radiolok/midi2aux/hw/kicad/analog_in.kicad_sch

## KiCad design hw/kicad/analog_in.kicad_sch (2026-10-06)

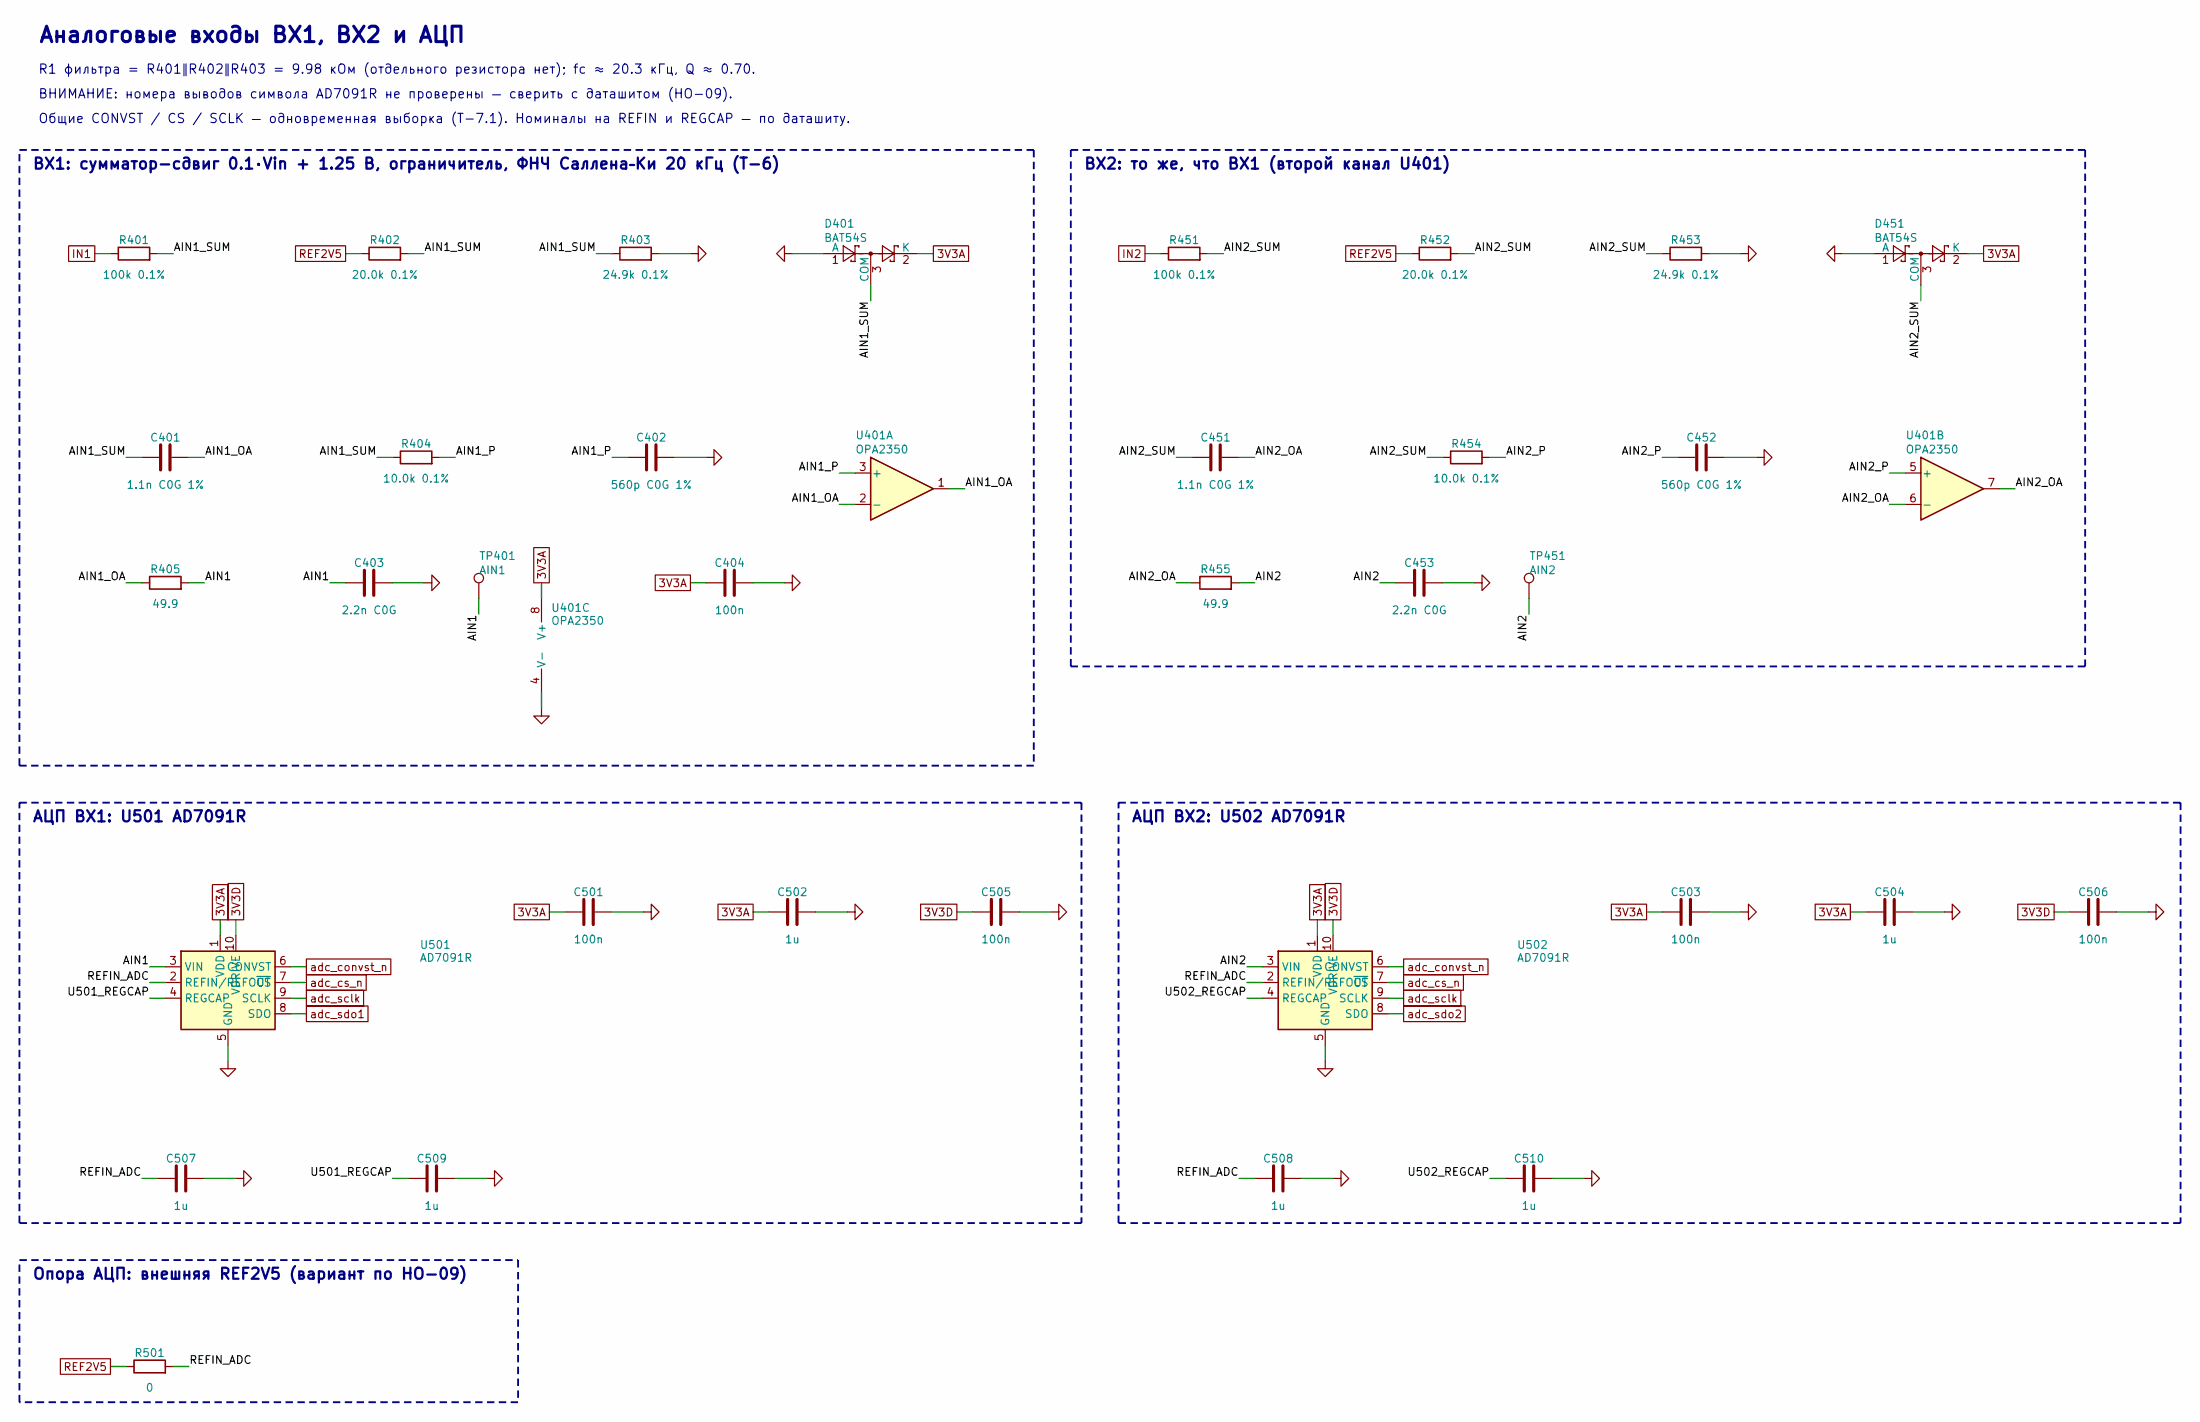
[picture p46: schematic analog_in.kicad_sch]

Parts:
C401, C451: 1.1n C0G 1%; C_0603_1608Metric
C402, C452: 560p C0G 1%; C_0603_1608Metric
C403, C453: 2.2n C0G; C_0603_1608Metric
C404, C501, C503, C505, C506: 100n; C_0603_1608Metric
C502, C504, C507, C508, C509, C510: 1u; C_0603_1608Metric
D401, D451: BAT54S; SOT-23
R401, R451: 100k 0.1%; R_0805_2012Metric
R402, R452: 20.0k 0.1%; R_0603_1608Metric
R403, R453: 24.9k 0.1%; R_0603_1608Metric
R404, R454: 10.0k 0.1%; R_0603_1608Metric
R405, R455: 49.9; R_0603_1608Metric
R501: 0; R_0603_1608Metric
TP401: AIN1; TestPoint_Pad_D1.5mm
TP451: AIN2; TestPoint_Pad_D1.5mm
U401: OPA2350; SOIC-8_3.9x4.9mm_P1.27mm
U501, U502: AD7091R; MSOP-10_3x3mm_P0.5mm

Connections:
3V3A: C404.1, C501.1, C502.1, C503.1, C504.1, D401.2 (K), D451.2 (K), U401.8 (V+), U501.1 (VDD), U502.1 (VDD)
3V3D: C505.1, C506.1, U501.10 (VDRIVE), U502.10 (VDRIVE)
AIN1: C403.1, R405.2, TP401.1, U501.3 (VIN)
AIN1_OA: C401.2, R405.1, U401.1, U401.2 (-)
AIN1_P: C402.1, R404.2, U401.3 (+)
AIN1_SUM: C401.1, D401.3 (COM), R401.2, R402.2, R403.1, R404.1
AIN2: C453.1, R455.2, TP451.1, U502.3 (VIN)
AIN2_OA: C451.2, R455.1, U401.6 (-), U401.7
AIN2_P: C452.1, R454.2, U401.5 (+)
AIN2_SUM: C451.1, D451.3 (COM), R451.2, R452.2, R453.1, R454.1
GND: C402.2, C403.2, C404.2, C452.2, C453.2, C501.2, C502.2, C503.2, C504.2, C505.2, C506.2, C507.2, C508.2, C509.2, C510.2, D401.1 (A), D451.1 (A), R403.2, R453.2, U401.4 (V-), U501.5 (GND), U502.5 (GND)
IN1: R401.1
IN2: R451.1
REF2V5: R402.1, R452.1, R501.1
REFIN_ADC: C507.1, C508.1, R501.2, U501.2 (REFIN/REFOUT), U502.2 (REFIN/REFOUT)
U501_REGCAP: C509.1, U501.4 (REGCAP)
U502_REGCAP: C510.1, U502.4 (REGCAP)
adc_convst_n: U501.6 (CONVST), U502.6 (CONVST)
adc_cs_n: U501.7 (~CS), U502.7 (~CS)
adc_sclk: U501.9 (SCLK), U502.9 (SCLK)
adc_sdo1: U501.8 (SDO)
adc_sdo2: U502.8 (SDO)

Notes on the sheet:
ВХ1: сумматор-сдвиг 0.1·Vin + 1.25 В, ограничитель, ФНЧ Саллена–Ки 20 кГц (Т-6)
ВХ2: то же, что ВХ1 (второй канал U401)
АЦП ВХ1: U501 AD7091R
АЦП ВХ2: U502 AD7091R
Опора АЦП: внешняя REF2V5 (вариант по HO-09)
Аналоговые входы ВХ1, ВХ2 и АЦП
R1 фильтра = R401‖R402‖R403 = 9.98 кОм (отдельного резистора нет); fc ≈ 20.3 кГц, Q ≈ 0.70.
ВНИМАНИЕ: номера выводов символа AD7091R не проверены — сверить с даташитом (HO-09).
Общие CONVST / CS / SCLK — одновременная выборка (Т-7.1). Номиналы на REFIN и REGCAP — по даташиту.
