radiolok/midi2aux/hw/kicad/audio_out.kicad_sch

## KiCad design hw/kicad/audio_out.kicad_sch (2026-10-06)

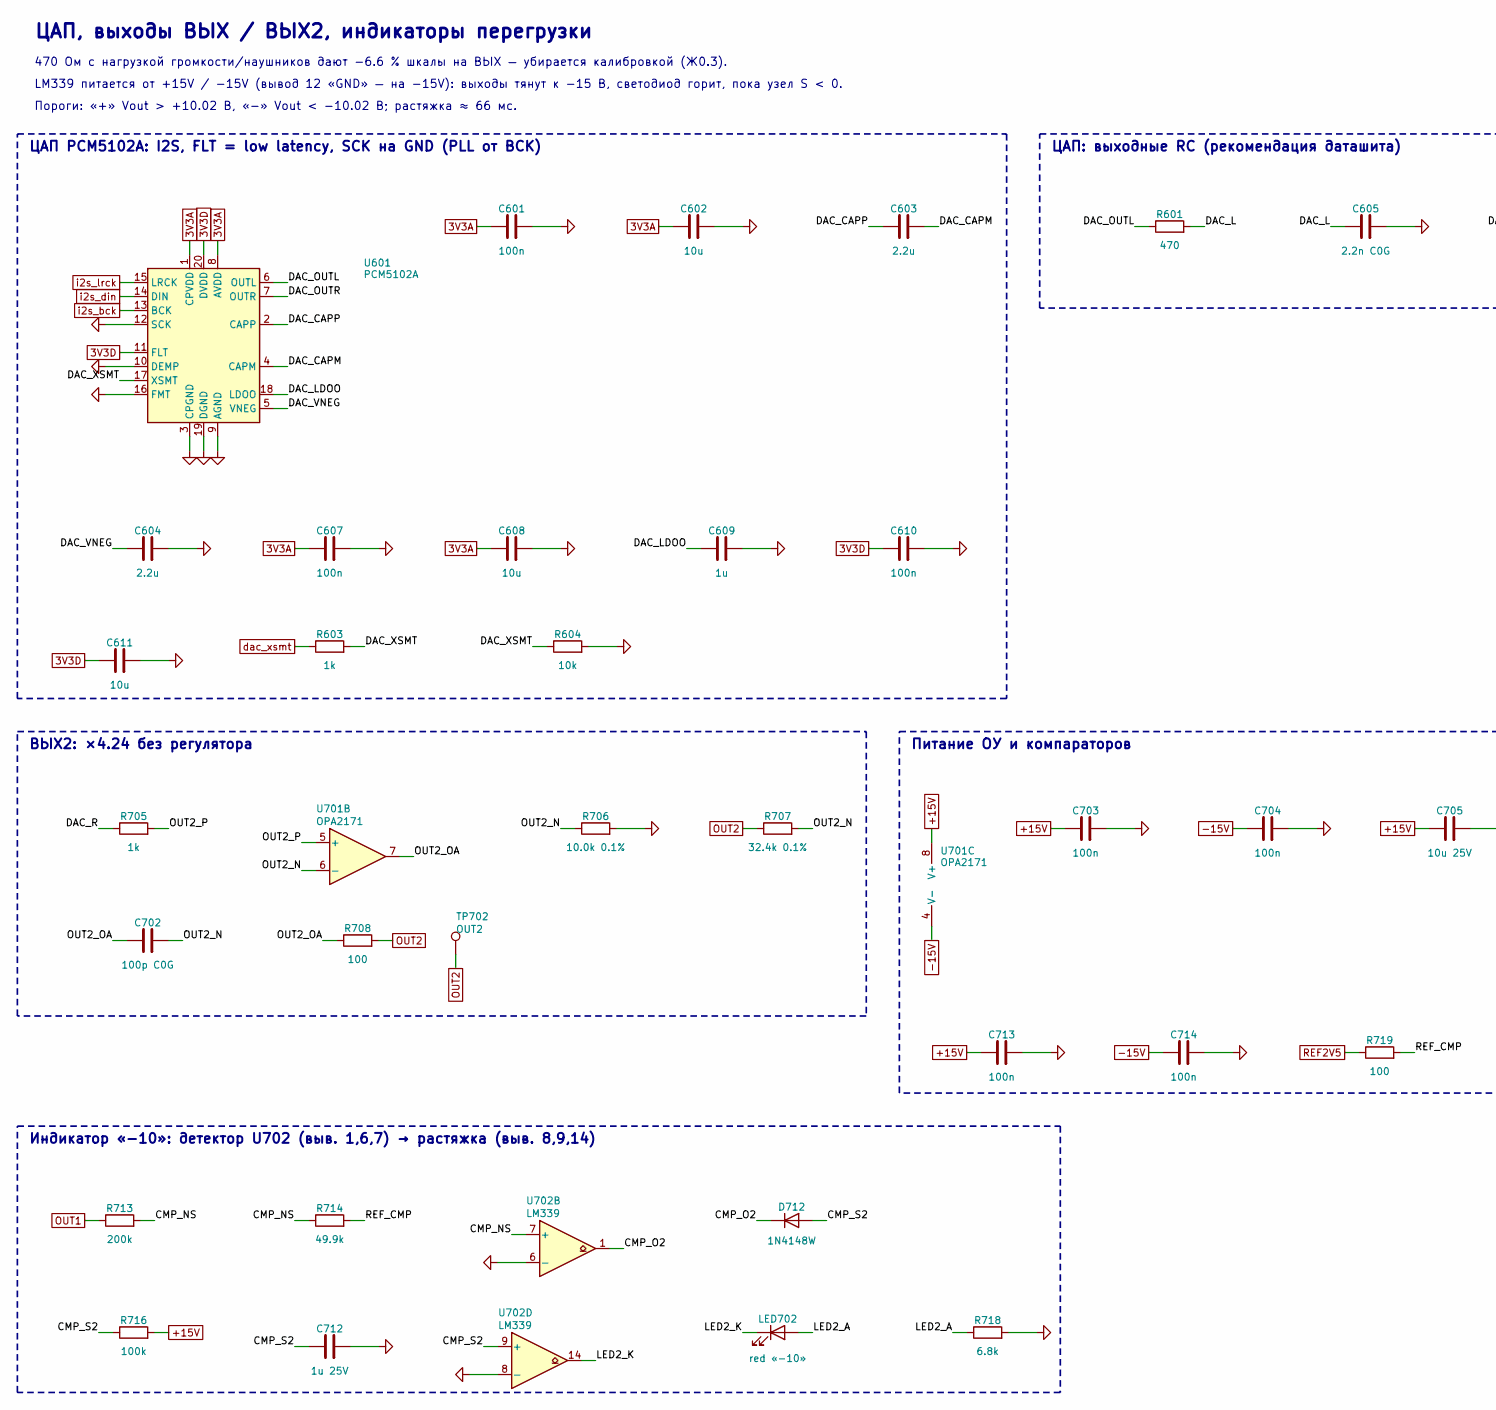
[picture p47: schematic audio_out.kicad_sch, part in row 1, column 1]

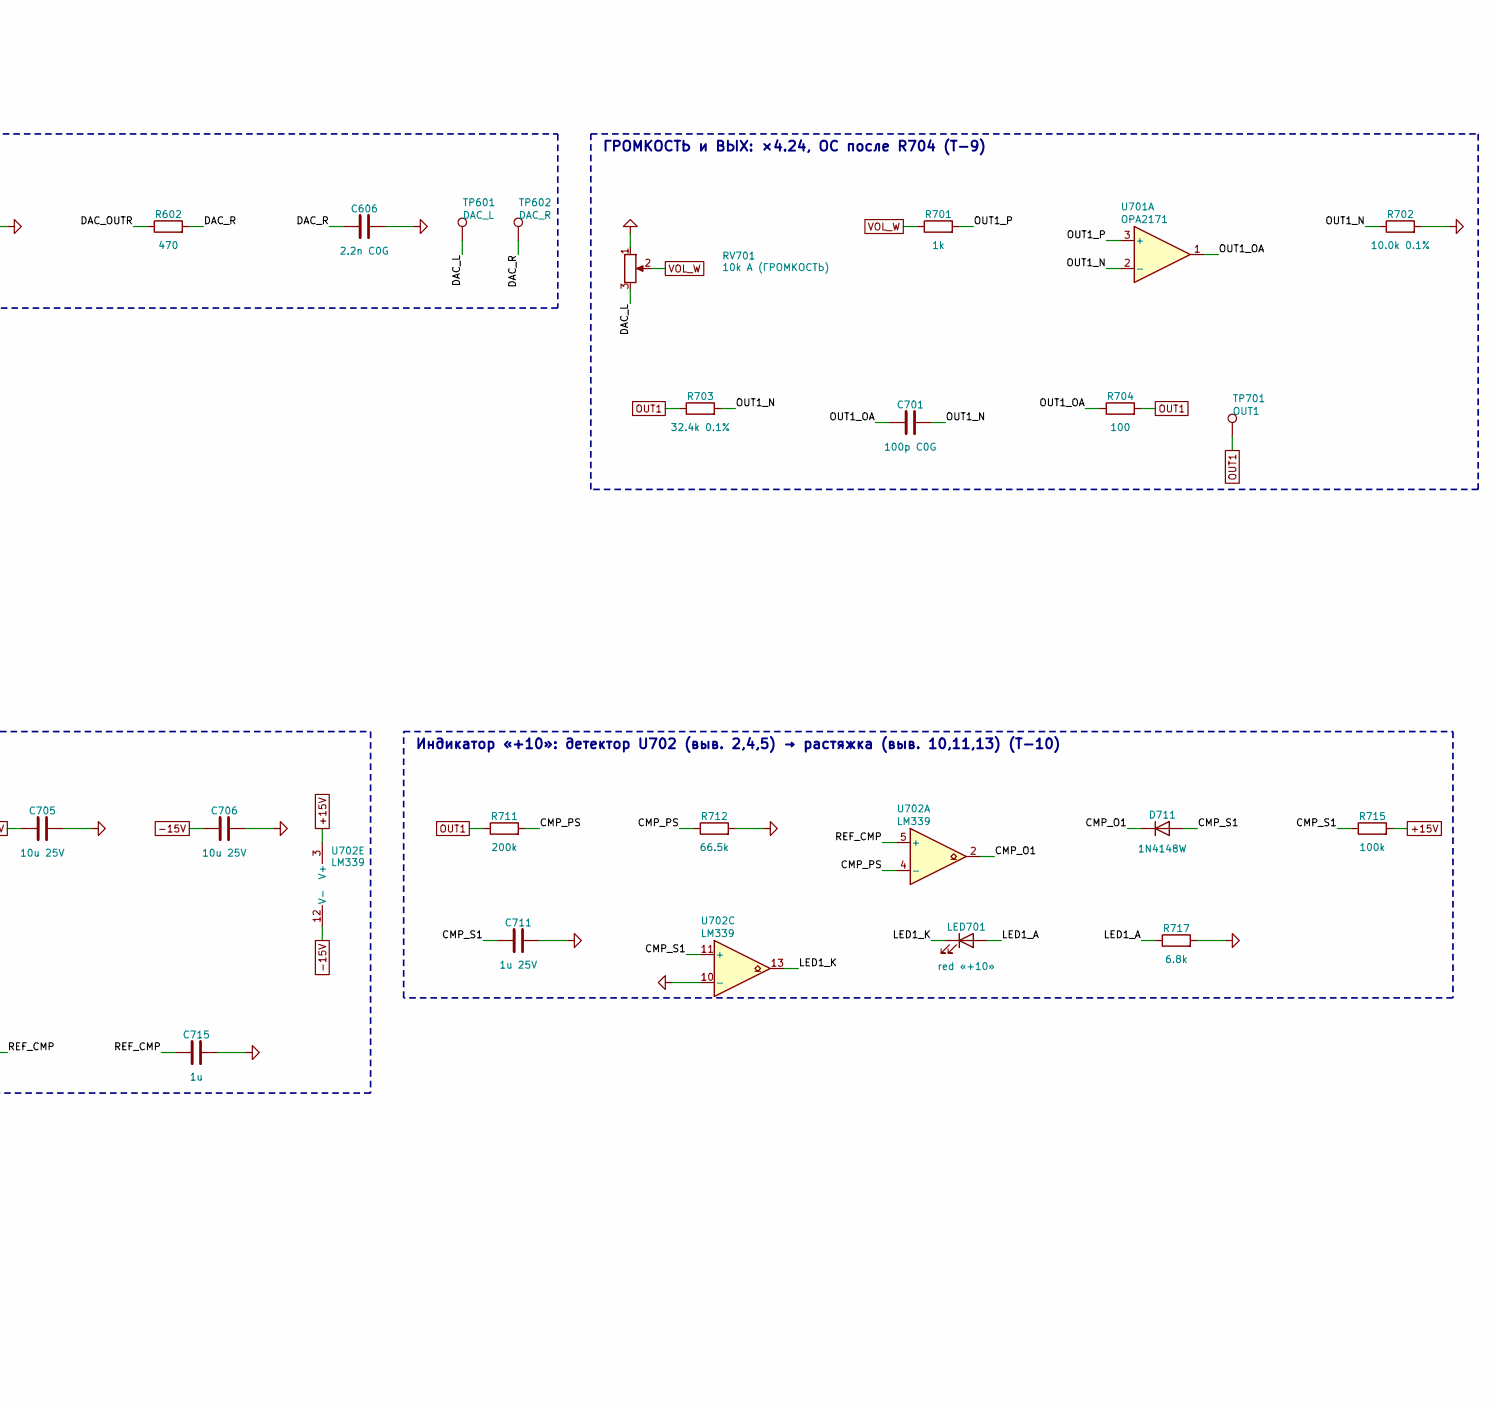
[picture p48: schematic audio_out.kicad_sch, part in row 1, column 2]

Parts:
C601, C607, C610, C703, C704, C713, C714: 100n; C_0603_1608Metric
C602, C608, C611: 10u; C_0805_2012Metric
C603, C604: 2.2u; C_0603_1608Metric
C605, C606: 2.2n C0G; C_0603_1608Metric
C609, C715: 1u; C_0603_1608Metric
C701, C702: 100p C0G; C_0603_1608Metric
C705, C706: 10u 25V; C_0805_2012Metric
C711, C712: 1u 25V; C_0805_2012Metric
D711, D712: 1N4148W; D_SOD-123
LED701: red «+10»; LED_D3.0mm
LED702: red «−10»; LED_D3.0mm
R601, R602: 470; R_0603_1608Metric
R603, R701, R705: 1k; R_0603_1608Metric
R604: 10k; R_0603_1608Metric
R702, R706: 10.0k 0.1%; R_0603_1608Metric
R703, R707: 32.4k 0.1%; R_0603_1608Metric
R704, R708: 100; R_0805_2012Metric
R711, R713: 200k; R_0603_1608Metric
R712: 66.5k; R_0603_1608Metric
R714: 49.9k; R_0603_1608Metric
R715, R716: 100k; R_0603_1608Metric
R717, R718: 6.8k; R_0603_1608Metric
R719: 100; R_0603_1608Metric
RV701: 10k A (ГРОМКОСТЬ); Potentiometer_Alps_RK09K_Single_Vertical
TP601: DAC_L; TestPoint_Pad_D1.5mm
TP602: DAC_R; TestPoint_Pad_D1.5mm
TP701: OUT1; TestPoint_Pad_D1.5mm
TP702: OUT2; TestPoint_Pad_D1.5mm
U601: PCM5102A; TSSOP-20_4.4x6.5mm_P0.65mm
U701: OPA2171; SOIC-8_3.9x4.9mm_P1.27mm
U702: LM339; SOIC-14_3.9x8.7mm_P1.27mm

Connections:
3V3A: C601.1, C602.1, C607.1, C608.1, U601.1 (CPVDD), U601.8 (AVDD)
3V3D: C610.1, C611.1, U601.11 (FLT), U601.20 (DVDD)
+15V: C703.1, C705.1, C713.1, R715.2, R716.2, U701.8 (V+), U702.3 (V+)
-15V: C704.1, C706.1, C714.1, U701.4 (V-), U702.12 (V-)
CMP_NS: R713.2, R714.1, U702.7 (+)
CMP_O1: D711.1 (K), U702.2
CMP_O2: D712.1 (K), U702.1
CMP_PS: R711.2, R712.1, U702.4 (-)
CMP_S1: C711.1, D711.2 (A), R715.1, U702.11 (+)
CMP_S2: C712.1, D712.2 (A), R716.1, U702.9 (+)
DAC_CAPM: C603.2, U601.4 (CAPM)
DAC_CAPP: C603.1, U601.2 (CAPP)
DAC_L: C605.1, R601.2, RV701.3, TP601.1
DAC_LDOO: C609.1, U601.18 (LDOO)
DAC_OUTL: R601.1, U601.6 (OUTL)
DAC_OUTR: R602.1, U601.7 (OUTR)
DAC_R: C606.1, R602.2, R705.1, TP602.1
DAC_VNEG: C604.1, U601.5 (VNEG)
GND: C601.2, C602.2, C604.2, C605.2, C606.2, C607.2, C608.2, C609.2, C610.2, C611.2, C703.2, C704.2, C705.2, C706.2, C711.2, C712.2, C713.2, C714.2, C715.2, R604.2, R702.2, R706.2, R712.2, R717.2, R718.2, RV701.1, U601.3 (CPGND), U601.9 (AGND), U601.10 (DEMP), U601.12 (SCK), U601.16 (FMT), U601.19 (DGND), U702.6 (-), U702.8 (-), U702.10 (-)
LED1_A: LED701.2 (A), R717.1
LED1_K: LED701.1 (K), U702.13
LED2_A: LED702.2 (A), R718.1
LED2_K: LED702.1 (K), U702.14
OUT1: R703.1, R704.2, R711.1, R713.1, TP701.1
OUT1_N: C701.2, R702.1, R703.2, U701.2 (-)
OUT1_OA: C701.1, R704.1, U701.1
OUT1_P: R701.2, U701.3 (+)
OUT2: R707.1, R708.2, TP702.1
OUT2_N: C702.2, R706.1, R707.2, U701.6 (-)
OUT2_OA: C702.1, R708.1, U701.7
OUT2_P: R705.2, U701.5 (+)
REF2V5: R719.1
REF_CMP: C715.1, R714.2, R719.2, U702.5 (+)
VOL_W: R701.1, RV701.2
dac_xsmt: R603.1, R603.2, R604.1, U601.17 (XSMT)
i2s_bck: U601.13 (BCK)
i2s_din: U601.14 (DIN)
i2s_lrck: U601.15 (LRCK)

Notes on the sheet:
ЦАП PCM5102A: I2S, FLT = low latency, SCK на GND (PLL от BCK)
ЦАП: выходные RC (рекомендация даташита)
ГРОМКОСТЬ и ВЫХ: ×4.24, ОС после R704 (Т-9)
ВЫХ2: ×4.24 без регулятора
Питание ОУ и компараторов
Индикатор «+10»: детектор U702 (выв. 2,4,5) → растяжка (выв. 10,11,13) (Т-10)
Индикатор «−10»: детектор U702 (выв. 1,6,7) → растяжка (выв. 8,9,14)
ЦАП, выходы ВЫХ / ВЫХ2, индикаторы перегрузки
470 Ом с нагрузкой громкости/наушников дают −6.6 % шкалы на ВЫХ — убирается калибровкой (Ж0.3).
LM339 питается от +15V / −15V (вывод 12 «GND» — на −15V): выходы тянут к −15 В, светодиод горит, пока узел S < 0.
Пороги: «+» Vout > +10.02 В, «−» Vout < −10.02 В; растяжка ≈ 66 мс.
