radiolok/midi2aux/hw/kicad/fpga.kicad_sch

## KiCad design hw/kicad/fpga.kicad_sch (2026-10-06)

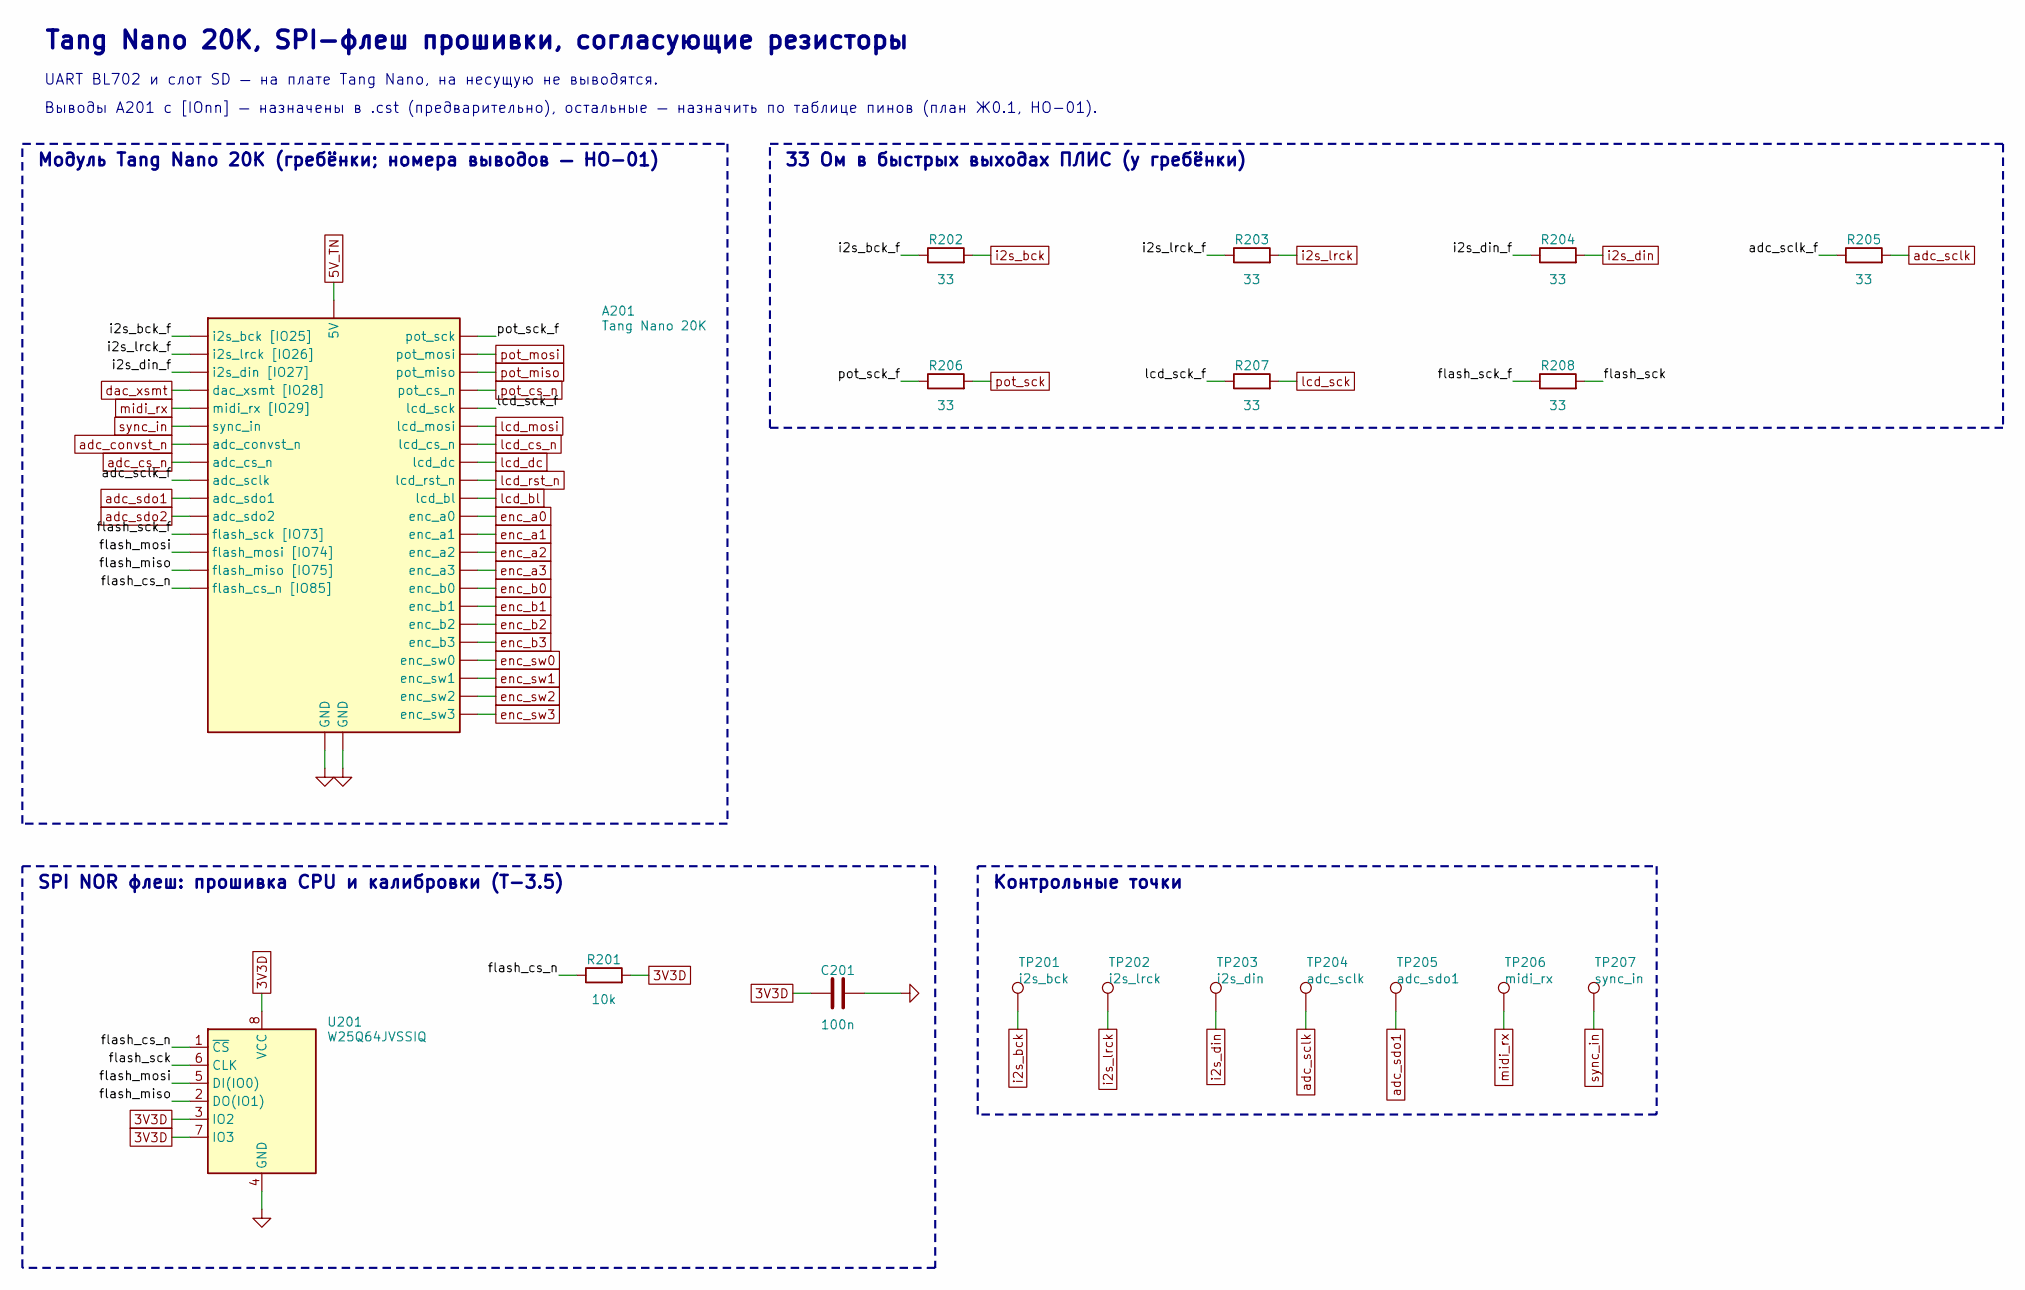
[picture p49: schematic fpga.kicad_sch]

Parts:
A201: Tang Nano 20K
C201: 100n; C_0603_1608Metric
R201: 10k; R_0603_1608Metric
R202, R203, R204, R205, R206, R207, R208: 33; R_0603_1608Metric
TP201: i2s_bck; TestPoint_Pad_D1.5mm
TP202: i2s_lrck; TestPoint_Pad_D1.5mm
TP203: i2s_din; TestPoint_Pad_D1.5mm
TP204: adc_sclk; TestPoint_Pad_D1.5mm
TP205: adc_sdo1; TestPoint_Pad_D1.5mm
TP206: midi_rx; TestPoint_Pad_D1.5mm
TP207: sync_in; TestPoint_Pad_D1.5mm
U201: W25Q64JVSSIQ; SOIC-8_3.9x4.9mm_P1.27mm

Connections:
3V3D: C201.1, R201.2, U201.3 (IO2), U201.7 (IO3), U201.8 (VCC)
5V_TN: A201.5V
GND: A201.GND1 (GND), A201.GND2 (GND), C201.2, U201.4 (GND)
adc_convst_n: A201.P_CNV (adc_convst_n)
adc_cs_n: A201.P_ACS (adc_cs_n)
adc_sclk: R205.2, TP204.1
adc_sclk_f: A201.P_ASCK (adc_sclk), R205.1
adc_sdo1: A201.P_SDO1 (adc_sdo1), TP205.1
adc_sdo2: A201.P_SDO2 (adc_sdo2)
dac_xsmt: A201.28 (dac_xsmt [IO28])
enc_a0: A201.P_EA0 (enc_a0)
enc_a1: A201.P_EA1 (enc_a1)
enc_a2: A201.P_EA2 (enc_a2)
enc_a3: A201.P_EA3 (enc_a3)
enc_b0: A201.P_EB0 (enc_b0)
enc_b1: A201.P_EB1 (enc_b1)
enc_b2: A201.P_EB2 (enc_b2)
enc_b3: A201.P_EB3 (enc_b3)
enc_sw0: A201.P_ES0 (enc_sw0)
enc_sw1: A201.P_ES1 (enc_sw1)
enc_sw2: A201.P_ES2 (enc_sw2)
enc_sw3: A201.P_ES3 (enc_sw3)
flash_cs_n: A201.85 (flash_cs_n [IO85]), R201.1, U201.1 (~CS)
flash_miso: A201.75 (flash_miso [IO75]), U201.2 (DO(IO1))
flash_mosi: A201.74 (flash_mosi [IO74]), U201.5 (DI(IO0))
flash_sck: R208.2, U201.6 (CLK)
flash_sck_f: A201.73 (flash_sck [IO73]), R208.1
i2s_bck: R202.2, TP201.1
i2s_bck_f: A201.25 (i2s_bck [IO25]), R202.1
i2s_din: R204.2, TP203.1
i2s_din_f: A201.27 (i2s_din [IO27]), R204.1
i2s_lrck: R203.2, TP202.1
i2s_lrck_f: A201.26 (i2s_lrck [IO26]), R203.1
lcd_bl: A201.P_LBL (lcd_bl)
lcd_cs_n: A201.P_LCS (lcd_cs_n)
lcd_dc: A201.P_LDC (lcd_dc)
lcd_mosi: A201.P_LMOSI (lcd_mosi)
lcd_rst_n: A201.P_LRST (lcd_rst_n)
lcd_sck: R207.2
lcd_sck_f: A201.P_LSCK (lcd_sck), R207.1
midi_rx: A201.29 (midi_rx [IO29]), TP206.1
pot_cs_n: A201.P_PCS (pot_cs_n)
pot_miso: A201.P_PMISO (pot_miso)
pot_mosi: A201.P_PMOSI (pot_mosi)
pot_sck: R206.2
pot_sck_f: A201.P_PSCK (pot_sck), R206.1
sync_in: A201.P_SYNC (sync_in), TP207.1

Notes on the sheet:
Модуль Tang Nano 20K (гребёнки; номера выводов — HO-01)
33 Ом в быстрых выходах ПЛИС (у гребёнки)
SPI NOR флеш: прошивка CPU и калибровки (Т-3.5)
Контрольные точки
Tang Nano 20K, SPI-флеш прошивки, согласующие резисторы
UART BL702 и слот SD — на плате Tang Nano, на несущую не выводятся.
Выводы A201 с [IOnn] — назначены в .cst (предварительно), остальные — назначить по таблице пинов (план Ж0.1, HO-01).
