radiolok/midi2aux/hw/kicad/midi_sync.kicad_sch

## KiCad design hw/kicad/midi_sync.kicad_sch (2026-10-06)

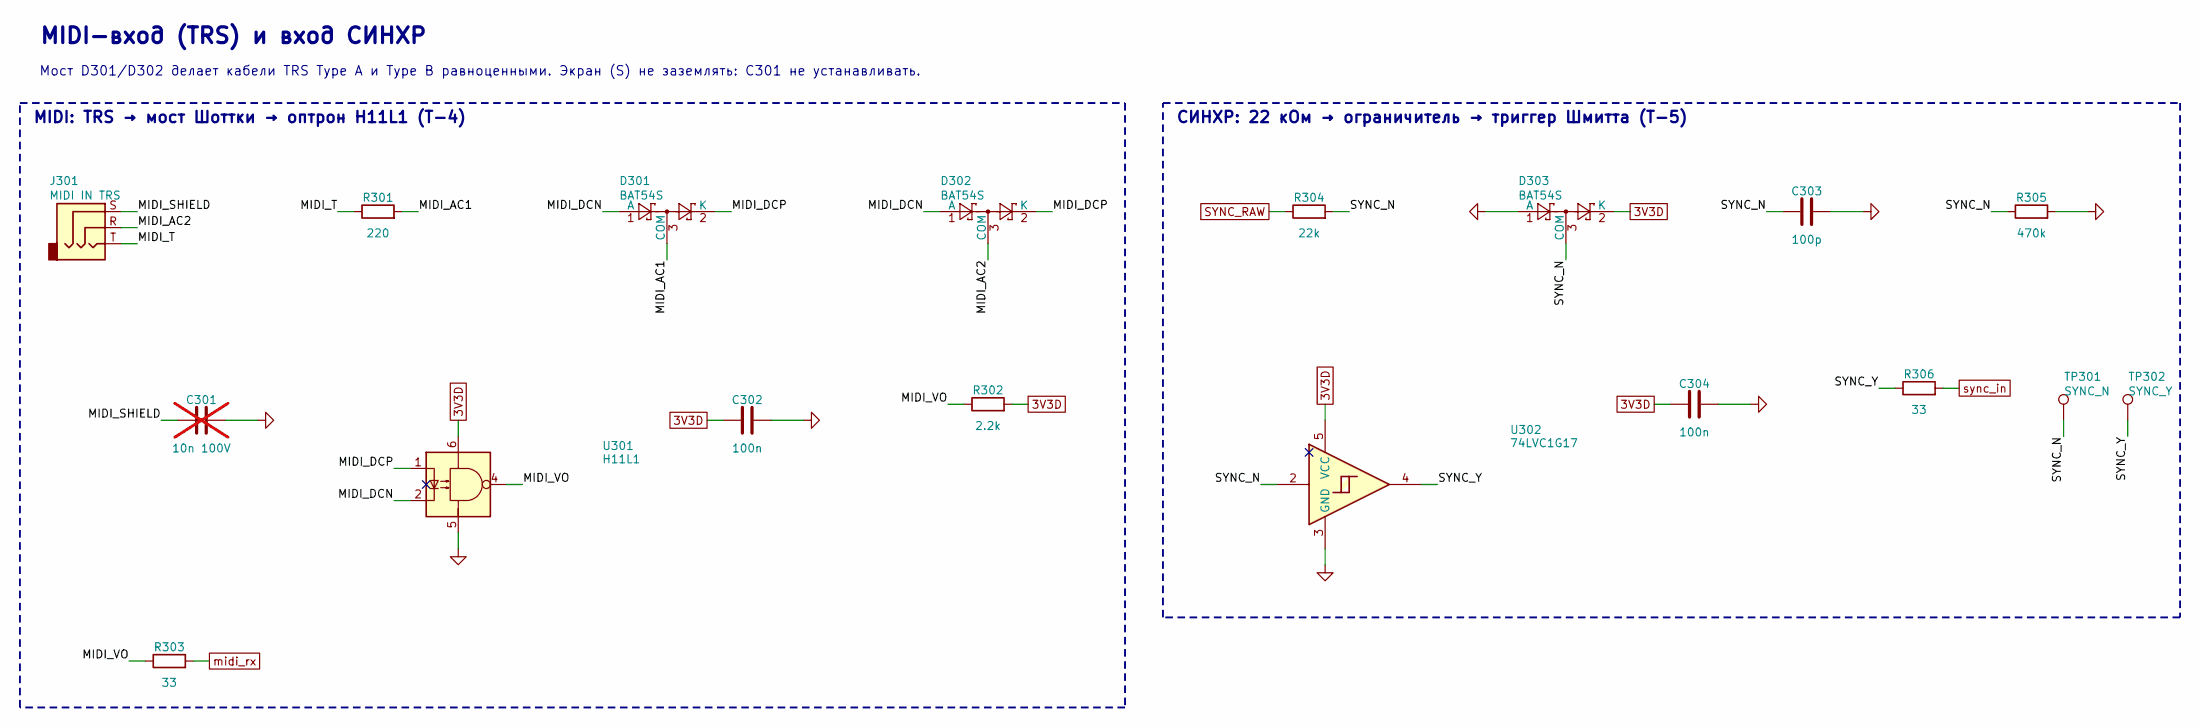
[picture p50: schematic midi_sync.kicad_sch]

Parts:
C301: 10n 100V; C_0603_1608Metric; not fitted
C302, C304: 100n; C_0603_1608Metric
C303: 100p; C_0603_1608Metric
D301, D302, D303: BAT54S; SOT-23
J301: MIDI IN TRS; Jack_3.5mm_Lumberg_1503_03_Horizontal
R301: 220; R_0603_1608Metric
R302: 2.2k; R_0603_1608Metric
R303, R306: 33; R_0603_1608Metric
R304: 22k; R_0603_1608Metric
R305: 470k; R_0603_1608Metric
TP301: SYNC_N; TestPoint_Pad_D1.5mm
TP302: SYNC_Y; TestPoint_Pad_D1.5mm
U301: H11L1; SMDIP-6_W9.53mm
U302: 74LVC1G17; SOT-23-5

Connections:
3V3D: C302.1, C304.1, D303.2 (K), R302.2, U301.6, U302.5 (VCC)
GND: C301.2, C302.2, C303.2, C304.2, D303.1 (A), R305.2, U301.5, U302.3 (GND)
MIDI_AC1: D301.3 (COM), R301.2
MIDI_AC2: D302.3 (COM), J301.R
MIDI_DCN: D301.1 (A), D302.1 (A), U301.2
MIDI_DCP: D301.2 (K), D302.2 (K), U301.1
MIDI_SHIELD: C301.1, J301.S
MIDI_T: J301.T, R301.1
MIDI_VO: R302.1, R303.1, U301.4
SYNC_N: C303.1, D303.3 (COM), R304.2, R305.1, TP301.1, U302.2
SYNC_RAW: R304.1
SYNC_Y: R306.1, TP302.1, U302.4
midi_rx: R303.2
sync_in: R306.2

Notes on the sheet:
MIDI: TRS → мост Шоттки → оптрон H11L1 (Т-4)
СИНХР: 22 кОм → ограничитель → триггер Шмитта (Т-5)
MIDI-вход (TRS) и вход СИНХР
Мост D301/D302 делает кабели TRS Type A и Type B равноценными. Экран (S) не заземлять: C301 не устанавливать.
