radiolok/midi2aux/hw/kicad/panel.kicad_sch

## KiCad design hw/kicad/panel.kicad_sch (2026-10-06)

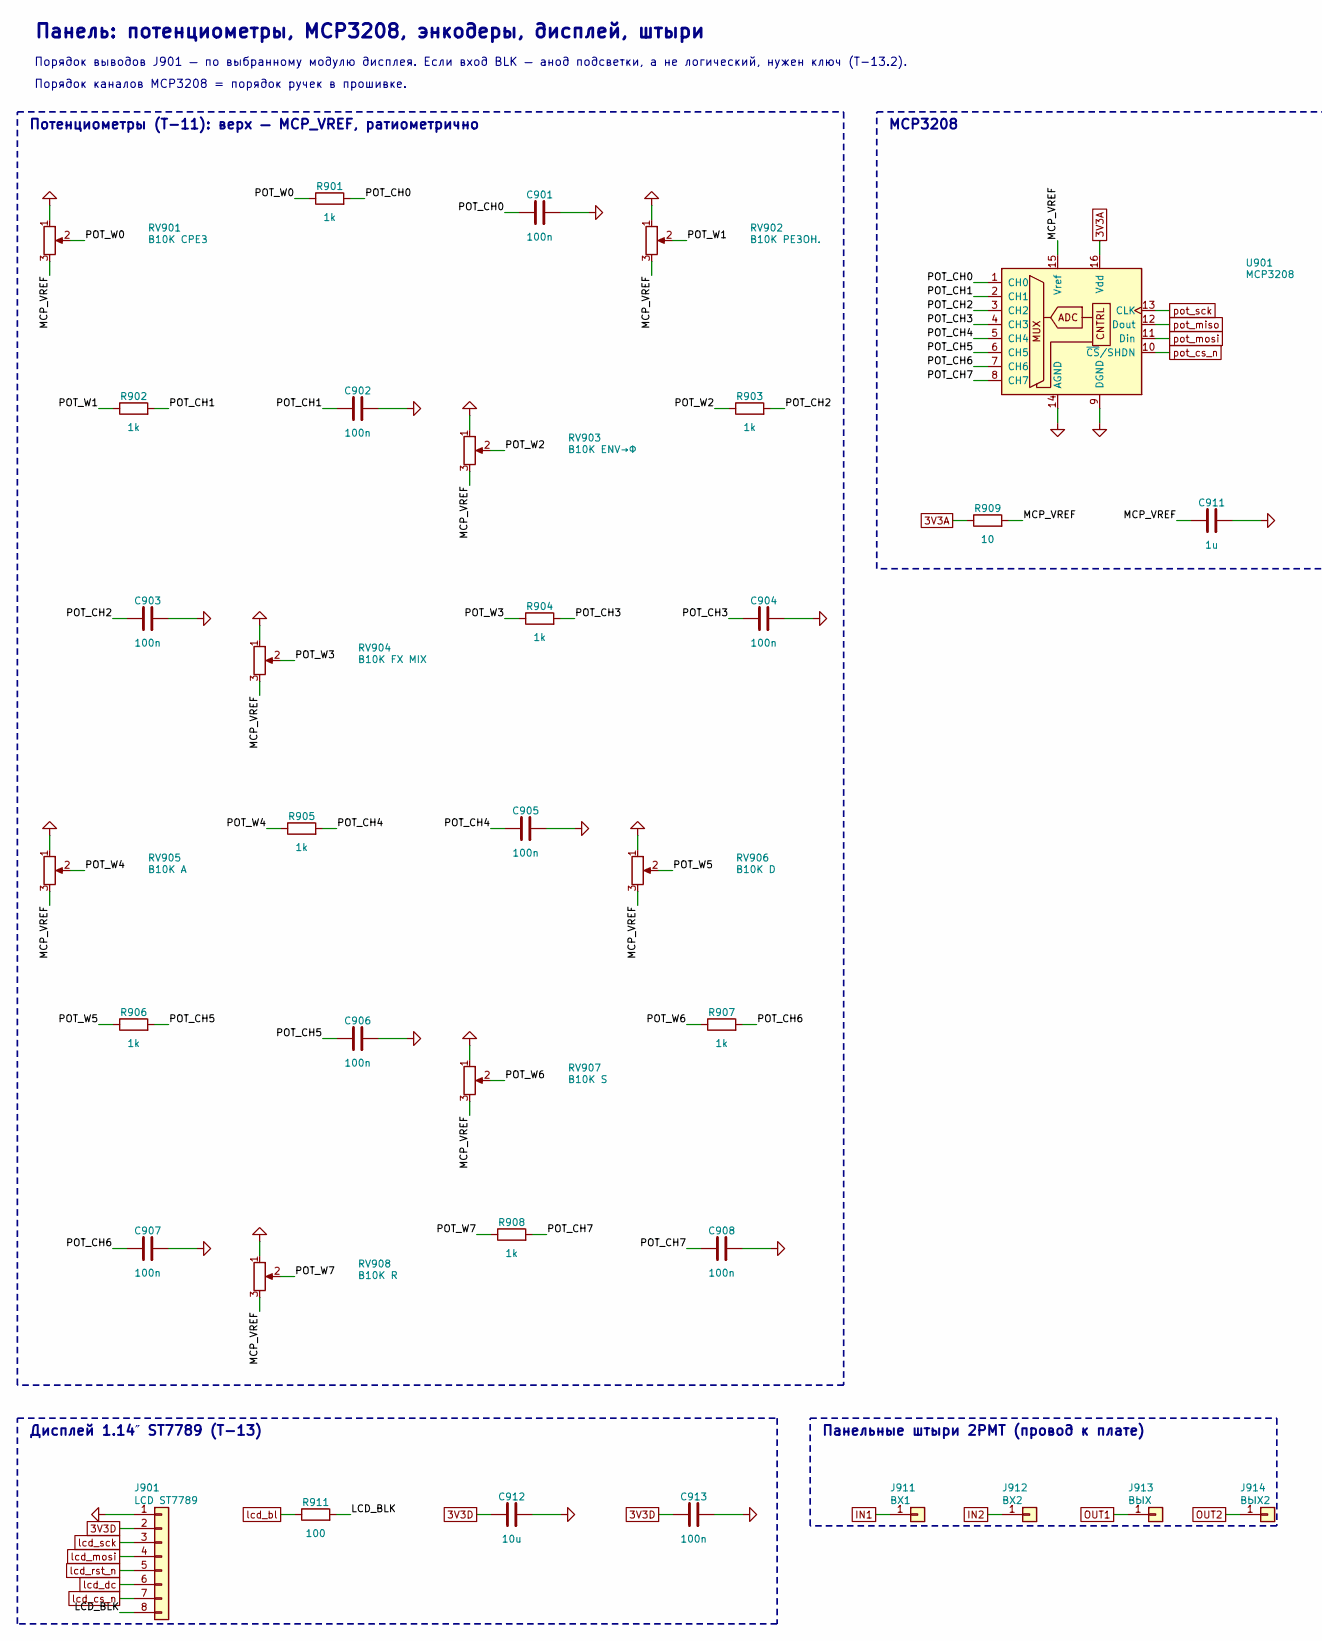
[picture p51: schematic panel.kicad_sch, part in row 1, column 1]

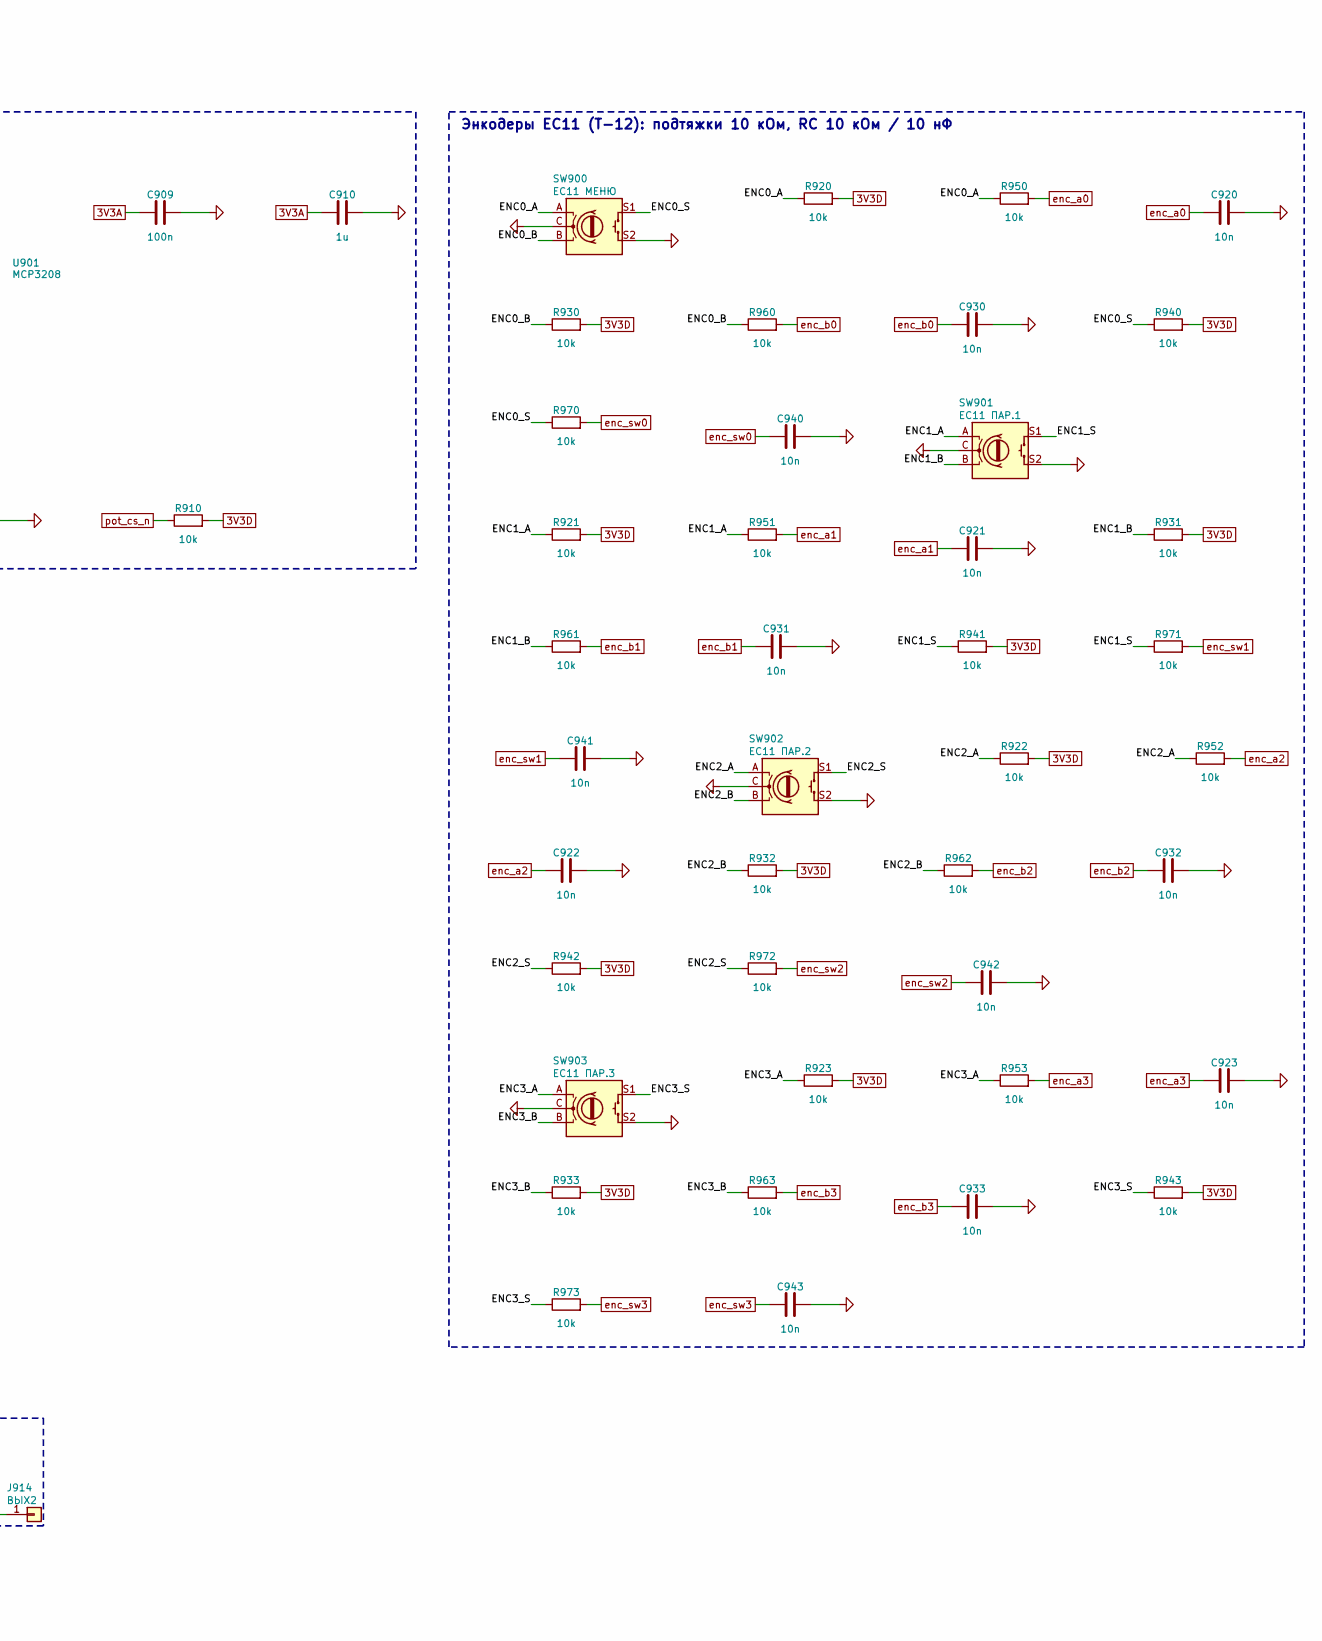
[picture p52: schematic panel.kicad_sch, part in row 1, column 2]

Parts:
C901, C902, C903, C904, C905, C906, C907, C908, C909, C913: 100n; C_0603_1608Metric
C910, C911: 1u; C_0603_1608Metric
C912: 10u; C_0805_2012Metric
C920, C921, C922, C923, C930, C931, C932, C933, C940, C941, C942, C943: 10n; C_0603_1608Metric
J901: LCD ST7789; PinSocket_1x08_P2.54mm_Vertical
J911: ВХ1; SolderWire-0.5sqmm_1x01_D0.9mm_OD2.1mm
J912: ВХ2; SolderWire-0.5sqmm_1x01_D0.9mm_OD2.1mm
J913: ВЫХ; SolderWire-0.5sqmm_1x01_D0.9mm_OD2.1mm
J914: ВЫХ2; SolderWire-0.5sqmm_1x01_D0.9mm_OD2.1mm
R901, R902, R903, R904, R905, R906, R907, R908: 1k; R_0603_1608Metric
R909: 10; R_0603_1608Metric
R910, R920, R921, R922, R923, R930, R931, R932, R933, R940, R941, R942, R943, R950, R951, R952, R953, R960, R961, R962, R963, R970, R971, R972, R973: 10k; R_0603_1608Metric
R911: 100; R_0603_1608Metric
RV901: B10K СРЕЗ; Potentiometer_Alps_RK09K_Single_Vertical
RV902: B10K РЕЗОН.; Potentiometer_Alps_RK09K_Single_Vertical
RV903: B10K ENV→Ф; Potentiometer_Alps_RK09K_Single_Vertical
RV904: B10K FX MIX; Potentiometer_Alps_RK09K_Single_Vertical
RV905: B10K A; Potentiometer_Alps_RK09K_Single_Vertical
RV906: B10K D; Potentiometer_Alps_RK09K_Single_Vertical
RV907: B10K S; Potentiometer_Alps_RK09K_Single_Vertical
RV908: B10K R; Potentiometer_Alps_RK09K_Single_Vertical
SW900: EC11 МЕНЮ; RotaryEncoder_Alps_EC11E-Switch_Vertical_H20mm
SW901: EC11 ПАР.1; RotaryEncoder_Alps_EC11E-Switch_Vertical_H20mm
SW902: EC11 ПАР.2; RotaryEncoder_Alps_EC11E-Switch_Vertical_H20mm
SW903: EC11 ПАР.3; RotaryEncoder_Alps_EC11E-Switch_Vertical_H20mm
U901: MCP3208; SOIC-16_3.9x9.9mm_P1.27mm

Connections:
3V3A: C909.1, C910.1, R909.1, U901.16 (Vdd)
3V3D: C912.1, C913.1, J901.2, R910.2, R920.2, R921.2, R922.2, R923.2, R930.2, R931.2, R932.2, R933.2, R940.2, R941.2, R942.2, R943.2
ENC0_A: R920.1, R950.1, SW900.A
ENC0_B: R930.1, R960.1, SW900.B
ENC0_S: R940.1, R970.1, SW900.S1
ENC1_A: R921.1, R951.1, SW901.A
ENC1_B: R931.1, R961.1, SW901.B
ENC1_S: R941.1, R971.1, SW901.S1
ENC2_A: R922.1, R952.1, SW902.A
ENC2_B: R932.1, R962.1, SW902.B
ENC2_S: R942.1, R972.1, SW902.S1
ENC3_A: R923.1, R953.1, SW903.A
ENC3_B: R933.1, R963.1, SW903.B
ENC3_S: R943.1, R973.1, SW903.S1
GND: C901.2, C902.2, C903.2, C904.2, C905.2, C906.2, C907.2, C908.2, C909.2, C910.2, C911.2, C912.2, C913.2, C920.2, C921.2, C922.2, C923.2, C930.2, C931.2, C932.2, C933.2, C940.2, C941.2, C942.2, C943.2, J901.1, RV901.1, RV902.1, RV903.1, RV904.1, RV905.1, RV906.1, RV907.1, RV908.1, SW900.C, SW900.S2, SW901.C, SW901.S2, SW902.C, SW902.S2, SW903.C, SW903.S2, U901.9 (DGND), U901.14 (AGND)
IN1: J911.1
IN2: J912.1
LCD_BLK: J901.8, R911.2
MCP_VREF: C911.1, R909.2, RV901.3, RV902.3, RV903.3, RV904.3, RV905.3, RV906.3, RV907.3, RV908.3, U901.15 (Vref)
OUT1: J913.1
OUT2: J914.1
POT_CH0: C901.1, R901.2, U901.1 (CH0)
POT_CH1: C902.1, R902.2, U901.2 (CH1)
POT_CH2: C903.1, R903.2, U901.3 (CH2)
POT_CH3: C904.1, R904.2, U901.4 (CH3)
POT_CH4: C905.1, R905.2, U901.5 (CH4)
POT_CH5: C906.1, R906.2, U901.6 (CH5)
POT_CH6: C907.1, R907.2, U901.7 (CH6)
POT_CH7: C908.1, R908.2, U901.8 (CH7)
POT_W0: R901.1, RV901.2
POT_W1: R902.1, RV902.2
POT_W2: R903.1, RV903.2
POT_W3: R904.1, RV904.2
POT_W4: R905.1, RV905.2
POT_W5: R906.1, RV906.2
POT_W6: R907.1, RV907.2
POT_W7: R908.1, RV908.2
enc_a0: C920.1, R950.2
enc_a1: C921.1, R951.2
enc_a2: C922.1, R952.2
enc_a3: C923.1, R953.2
enc_b0: C930.1, R960.2
enc_b1: C931.1, R961.2
enc_b2: C932.1, R962.2
enc_b3: C933.1, R963.2
enc_sw0: C940.1, R970.2
enc_sw1: C941.1, R971.2
enc_sw2: C942.1, R972.2
enc_sw3: C943.1, R973.2
lcd_bl: R911.1
lcd_cs_n: J901.7
lcd_dc: J901.6
lcd_mosi: J901.4
lcd_rst_n: J901.5
lcd_sck: J901.3
pot_cs_n: R910.1, U901.10 (~CS/SHDN)
pot_miso: U901.12 (Dout)
pot_mosi: U901.11 (Din)
pot_sck: U901.13 (CLK)

Notes on the sheet:
Потенциометры (Т-11): верх — MCP_VREF, ратиометрично
MCP3208
Энкодеры EC11 (Т-12): подтяжки 10 кОм, RC 10 кОм / 10 нФ
Дисплей 1.14″ ST7789 (Т-13)
Панельные штыри 2РМТ (провод к плате)
Панель: потенциометры, MCP3208, энкодеры, дисплей, штыри
Порядок выводов J901 — по выбранному модулю дисплея. Если вход BLK — анод подсветки, а не логический, нужен ключ (Т-13.2).
Порядок каналов MCP3208 = порядок ручек в прошивке.
