radiolok/midi2aux/hw/kicad/phones.kicad_sch

## KiCad design hw/kicad/phones.kicad_sch (2026-10-06)

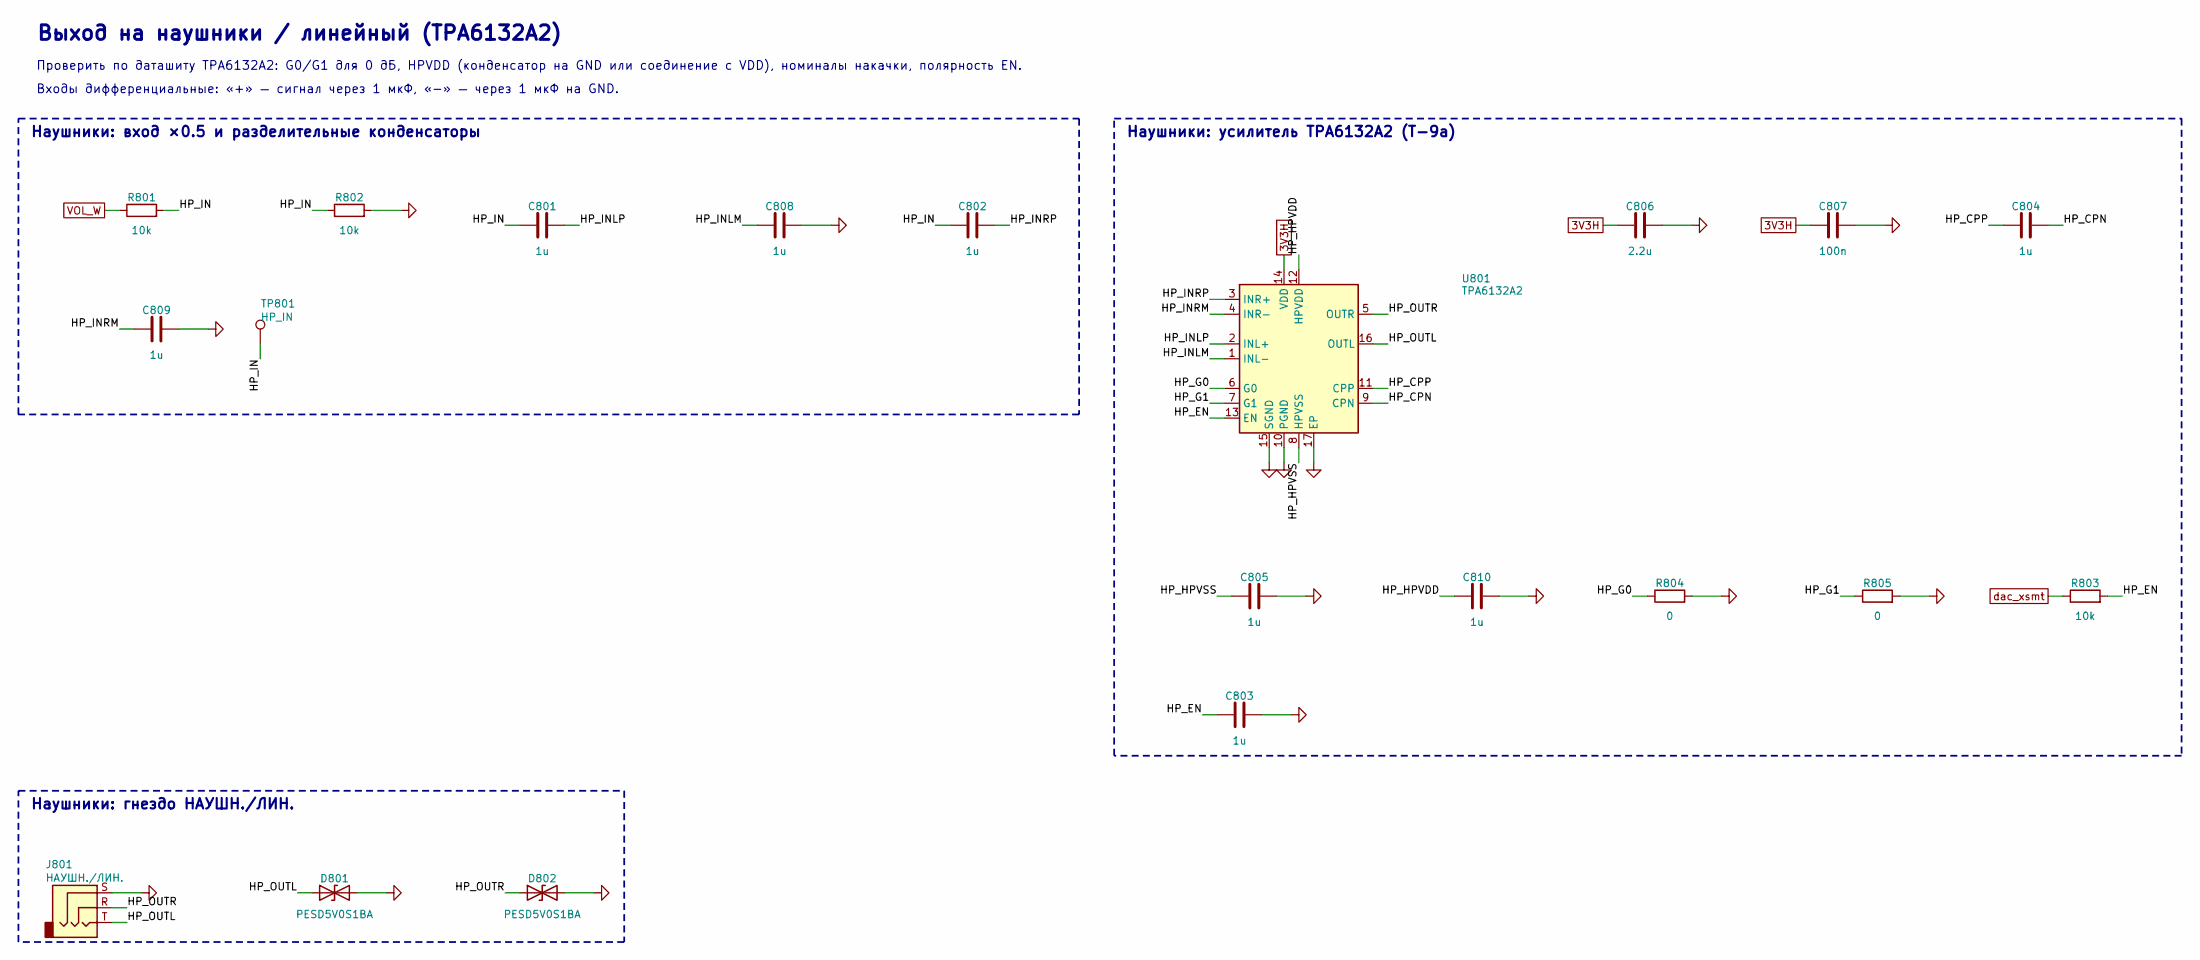
[picture p53: schematic phones.kicad_sch]

Parts:
C801, C802, C808, C809: 1u; C_0805_2012Metric
C803, C804, C805, C810: 1u; C_0603_1608Metric
C806: 2.2u; C_0603_1608Metric
C807: 100n; C_0603_1608Metric
D801, D802: PESD5V0S1BA; D_SOD-323
J801: НАУШН./ЛИН.; Jack_3.5mm_Lumberg_1503_03_Horizontal
R801, R802, R803: 10k; R_0603_1608Metric
R804, R805: 0; R_0603_1608Metric
TP801: HP_IN; TestPoint_Pad_D1.5mm
U801: TPA6132A2; WQFN-16-1EP_3x3mm_P0.5mm_EP1.68x1.68mm

Connections:
3V3H: C806.1, C807.1, U801.14 (VDD)
GND: C803.2, C805.2, C806.2, C807.2, C808.2, C809.2, C810.2, D801.2 (A2), D802.2 (A2), J801.S, R802.2, R804.2, R805.2, U801.10 (PGND), U801.15 (SGND), U801.17 (EP)
HP_CPN: C804.2, U801.9 (CPN)
HP_CPP: C804.1, U801.11 (CPP)
HP_EN: C803.1, R803.2, U801.13 (EN)
HP_G0: R804.1, U801.6 (G0)
HP_G1: R805.1, U801.7 (G1)
HP_HPVDD: C810.1, U801.12 (HPVDD)
HP_HPVSS: C805.1, U801.8 (HPVSS)
HP_IN: C801.1, C802.1, R801.2, R802.1, TP801.1
HP_INLM: C808.1, U801.1 (INL-)
HP_INLP: C801.2, U801.2 (INL+)
HP_INRM: C809.1, U801.4 (INR-)
HP_INRP: C802.2, U801.3 (INR+)
HP_OUTL: D801.1 (A1), J801.T, U801.16 (OUTL)
HP_OUTR: D802.1 (A1), J801.R, U801.5 (OUTR)
VOL_W: R801.1
dac_xsmt: R803.1

Notes on the sheet:
Наушники: вход ×0.5 и разделительные конденсаторы
Наушники: усилитель TPA6132A2 (Т-9a)
Наушники: гнездо НАУШН./ЛИН.
Выход на наушники / линейный (TPA6132A2)
Проверить по даташиту TPA6132A2: G0/G1 для 0 дБ, HPVDD (конденсатор на GND или соединение с VDD), номиналы накачки, полярность EN.
Входы дифференциальные: «+» — сигнал через 1 мкФ, «−» — через 1 мкФ на GND.
