radiolok/midi2aux/hw/kicad/power.kicad_sch

## KiCad design hw/kicad/power.kicad_sch (2026-10-06)

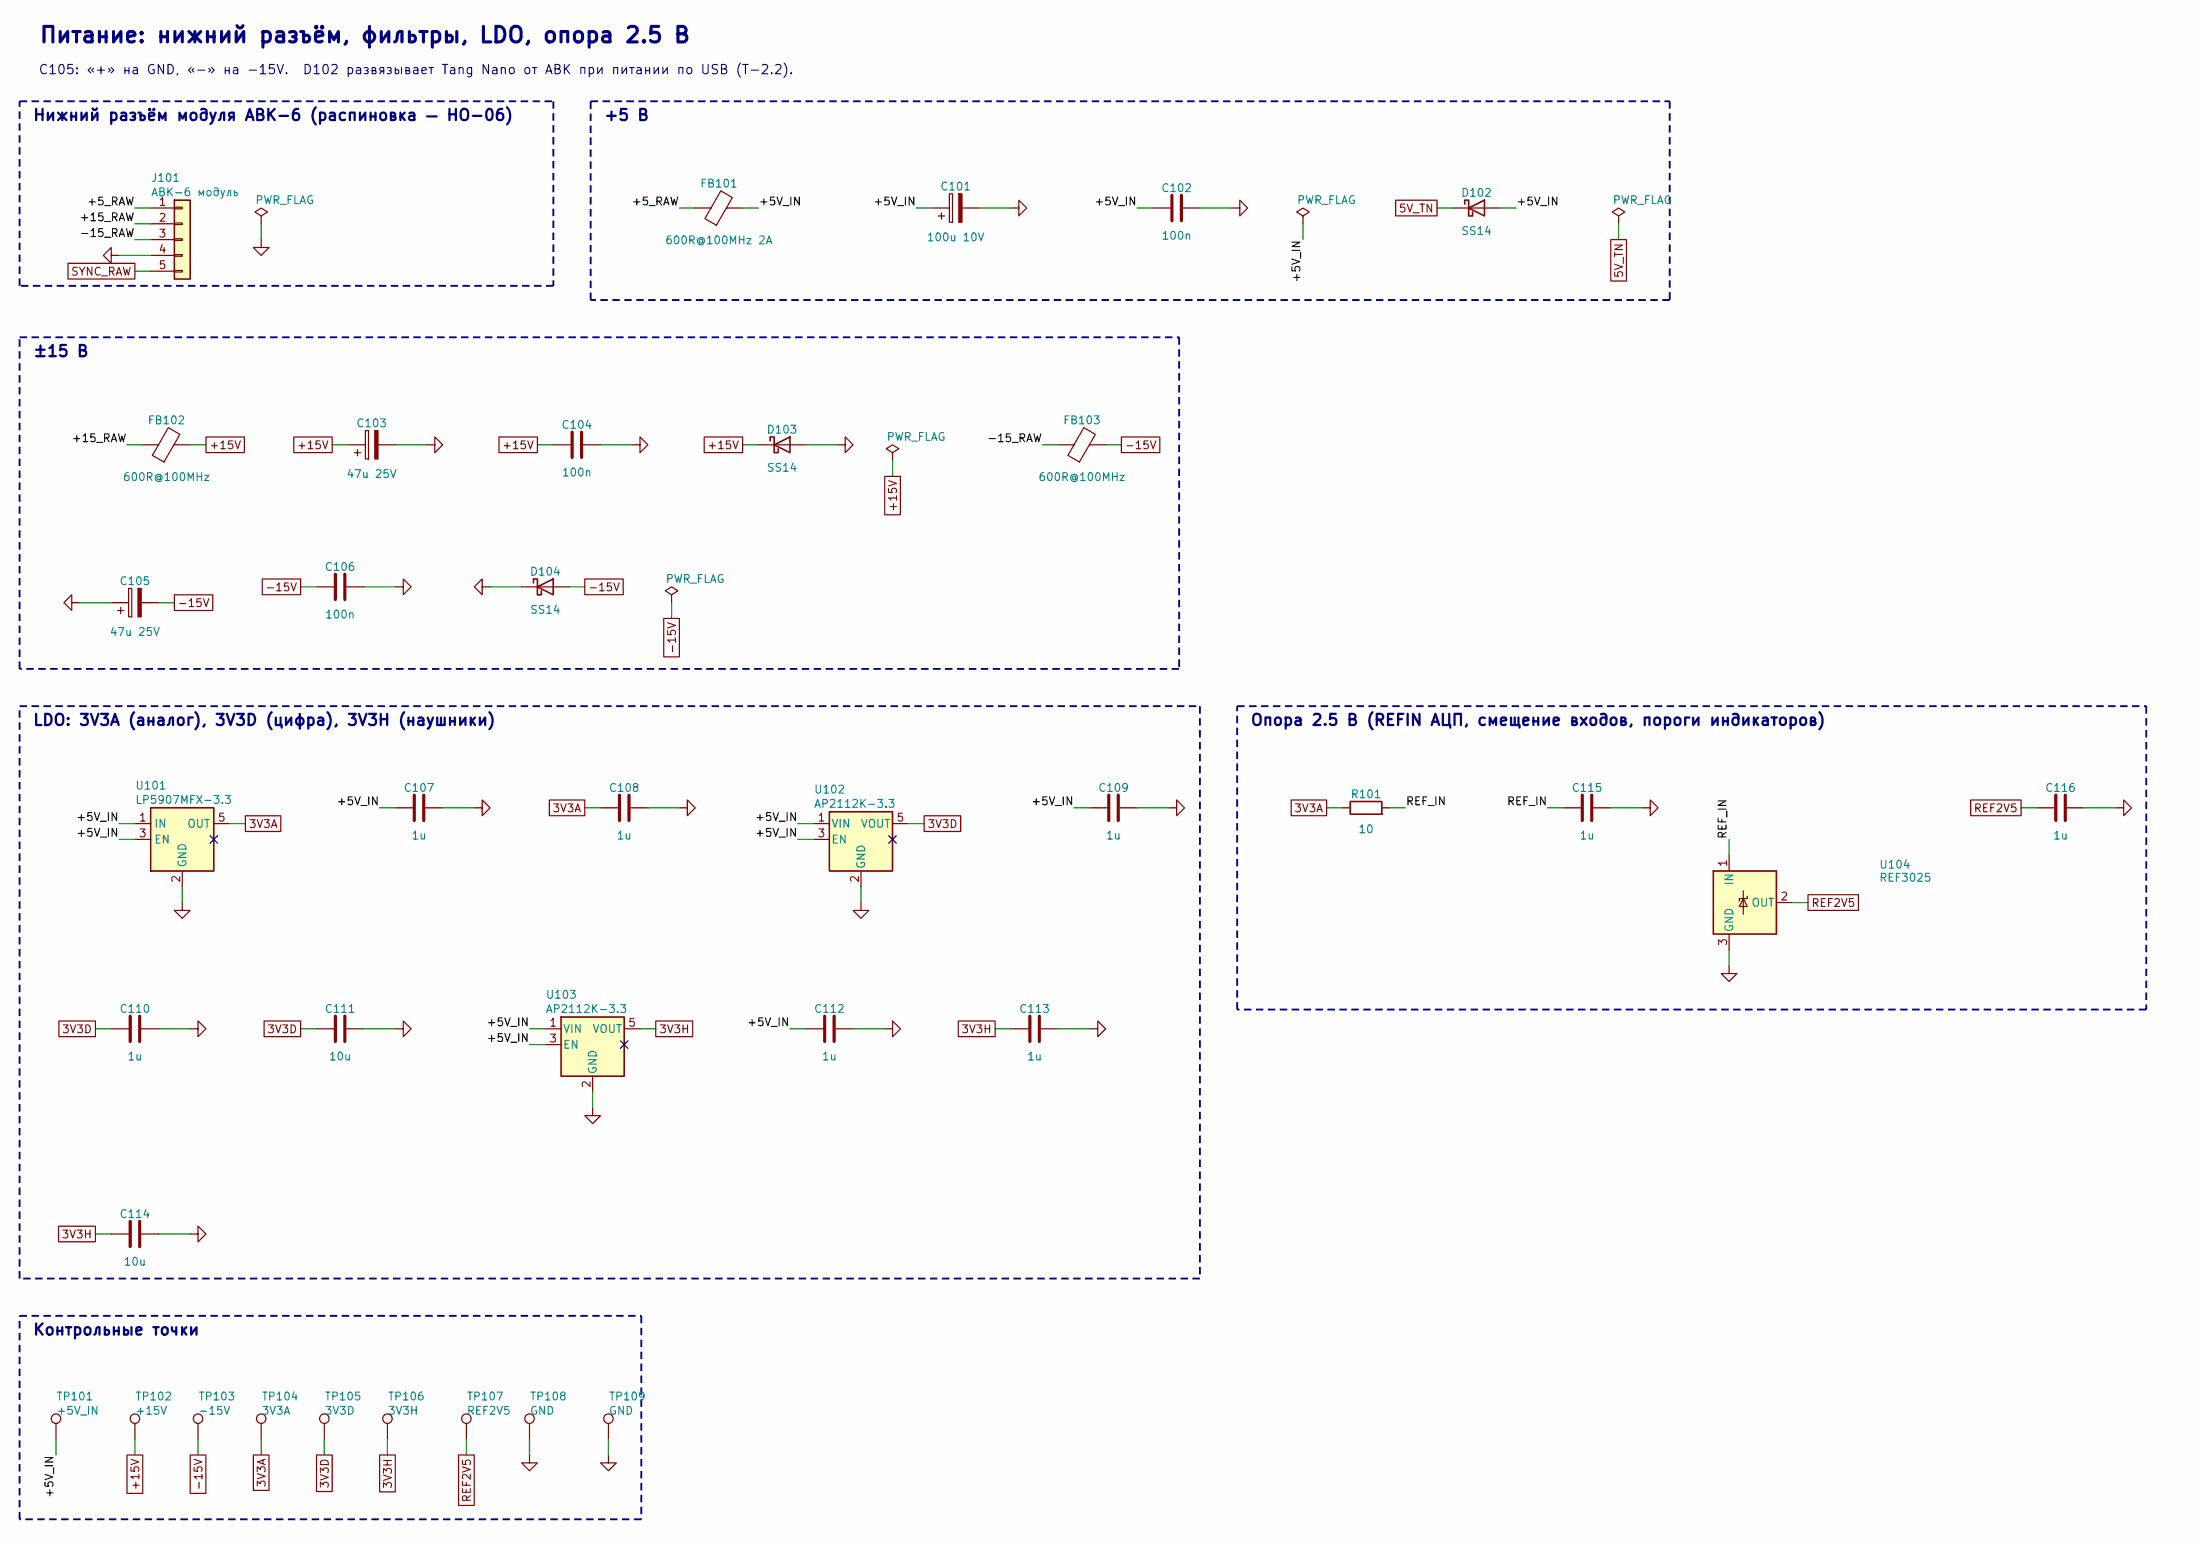
[picture p54: schematic power.kicad_sch]

Parts:
C101: 100u 10V; CP_Elec_6.3x5.4
C102, C104, C106: 100n; C_0603_1608Metric
C103, C105: 47u 25V; CP_Elec_6.3x5.4
C107, C108, C109, C110, C112, C113, C115, C116: 1u; C_0603_1608Metric
C111, C114: 10u; C_0805_2012Metric
D102, D103, D104: SS14; D_SMA
FB101: 600R@100MHz 2A; L_0805_2012Metric
FB102, FB103: 600R@100MHz; L_0805_2012Metric
J101: АВК-6 модуль
R101: 10; R_0603_1608Metric
TP101: +5V_IN; TestPoint_Pad_D1.5mm
TP102: +15V; TestPoint_Pad_D1.5mm
TP103: -15V; TestPoint_Pad_D1.5mm
TP104: 3V3A; TestPoint_Pad_D1.5mm
TP105: 3V3D; TestPoint_Pad_D1.5mm
TP106: 3V3H; TestPoint_Pad_D1.5mm
TP107: REF2V5; TestPoint_Pad_D1.5mm
TP108, TP109: GND; TestPoint_Pad_D1.5mm
U101: LP5907MFX-3.3; SOT-23-5
U102, U103: AP2112K-3.3; SOT-23-5
U104: REF3025; SOT-23

Connections:
3V3A: C108.1, R101.1, TP104.1, U101.5 (OUT)
3V3D: C110.1, C111.1, TP105.1, U102.5 (VOUT)
3V3H: C113.1, C114.1, TP106.1, U103.5 (VOUT)
5V_TN: D102.1 (K)
+5V_IN: C101.1, C102.1, C107.1, C109.1, C112.1, D102.2 (A), FB101.2, TP101.1, U101.1 (IN), U101.3 (EN), U102.1 (VIN), U102.3 (EN), U103.1 (VIN), U103.3 (EN)
+5_RAW: FB101.1, J101.1
+15V: C103.1, C104.1, D103.1 (K), FB102.2, TP102.1
+15_RAW: FB102.1, J101.2
-15V: C105.2, C106.1, D104.2 (A), FB103.2, TP103.1
-15_RAW: FB103.1, J101.3
GND: C101.2, C102.2, C103.2, C104.2, C105.1, C106.2, C107.2, C108.2, C109.2, C110.2, C111.2, C112.2, C113.2, C114.2, C115.2, C116.2, D103.2 (A), D104.1 (K), J101.4, TP108.1, TP109.1, U101.2 (GND), U102.2 (GND), U103.2 (GND), U104.3 (GND)
REF2V5: C116.1, TP107.1, U104.2 (OUT)
REF_IN: C115.1, R101.2, U104.1 (IN)
SYNC_RAW: J101.5

Notes on the sheet:
Нижний разъём модуля АВК-6 (распиновка — HO-06)
+5 В
±15 В
LDO: 3V3A (аналог), 3V3D (цифра), 3V3H (наушники)
Опора 2.5 В (REFIN АЦП, смещение входов, пороги индикаторов)
Контрольные точки
Питание: нижний разъём, фильтры, LDO, опора 2.5 В
C105: «+» на GND, «−» на −15V. D102 развязывает Tang Nano от АВК при питании по USB (Т-2.2).
