radiolok/midi2aux/sw/fw/synth.h

/* Synth control: MIDI events -> voice allocation -> engine / modulation registers.
 * Register access goes through hw_write / hw_read so the logic is host-testable. */
#ifndef SYNTH_H
#define SYNTH_H

#include <stdint.h>

#include "params.h"
#include "patch.h"
#include "voice_alloc.h"

#define MOD_ROUTES 8
#define AVK_MAX_SLOTS 8 /* hardware slots looked at */
#define AVK_PATCH_SLOTS 2 /* MATH and DELAY slots the patch configures (P_SLOTn_*, P_DLYn_*) */
struct mod_route {
    uint8_t src, via, dst;
    int32_t depth; /* raw register value: pitch units (PM/CM) or Q16 (AM/PW) */
};

struct synth {
    struct voice_alloc va;
    struct fs_info fs;
    uint32_t p_a4;
    int nvoices;
    struct patch p;
    uint8_t retrig[VA_MAX_VOICES]; /* retrigger toggle bit per voice */
    uint8_t mod_wheel;
    int16_t bend;
    struct mod_route routes[MOD_ROUTES];
    int nslots;                    /* effect slots in the hardware */
    uint8_t slot_type[AVK_MAX_SLOTS];
    int8_t math_slot[AVK_PATCH_SLOTS], dly_slot[AVK_PATCH_SLOTS]; /* hardware index, -1 none */
    int8_t cho_slot, rev_slot;
    uint32_t sync_samples;         /* SYNC period in samples, 0 unknown */
    uint32_t sync_edges;           /* last seen SYNC edge count */
    int sync_note;                 /* note held by SYNC_NOTE mode, -1 none */
};

void hw_write(uint32_t addr, uint32_t val);
uint32_t hw_read(uint32_t addr);

void synth_init(struct synth *s, int nvoices, struct fs_info fs);
void synth_apply_patch(struct synth *s);
void synth_set_param(struct synth *s, int id, int32_t value);
/* one event from the MIDI FIFO (status, d1, d2); returns the voice touched or -1 */
int synth_midi(struct synth *s, uint8_t st, uint8_t d1, uint8_t d2);
void synth_all_off(struct synth *s);
/* route 0 is the vibrato route (LFO1 x mod wheel -> pitch), routes 1..7 are free */
void synth_set_route(struct synth *s, int k, struct mod_route r);

/* AVK link (avk.c): bus, slots, OUT2, SYNC, input calibration */
void avk_init(struct synth *s);
void avk_apply(struct synth *s);
/* call from the main loop: SYNC edges -> notes in SYNC_NOTE mode; returns 1 on a new edge */
int avk_poll(struct synth *s);
/* input i (0, 1): the current input is 0 V -> OFFSET = current code */
void avk_cal_zero(int i);
/* the current input is mv millivolts -> GAIN; returns 0 if the code equals the offset */
int avk_cal_ref(int i, int32_t mv);
/* OUT2 pitch CV for a note (1 V/octave, C4 = 0 V), Q2.16 */
int32_t avk_pitch_cv(int note);
/* SYNC frequency in 0.01 Hz, 0 if unknown */
uint32_t avk_sync_hz100(const struct synth *s);

#endif
