radiolok/midi2aux/fw/src/midi.h

#ifndef MIDI_H
#define MIDI_H

#include <avr/io.h>

void midiParser(uint8_t byte);
uint16_t getNotePeriod(uint8_t note);
void noteOn(uint8_t note);
void noteOff(void);

extern volatile uint8_t midiActive;

#endif
